devEmbedded/differential_probe/accessories/cable_to_banana/images/cable_to_banana_bottom.png

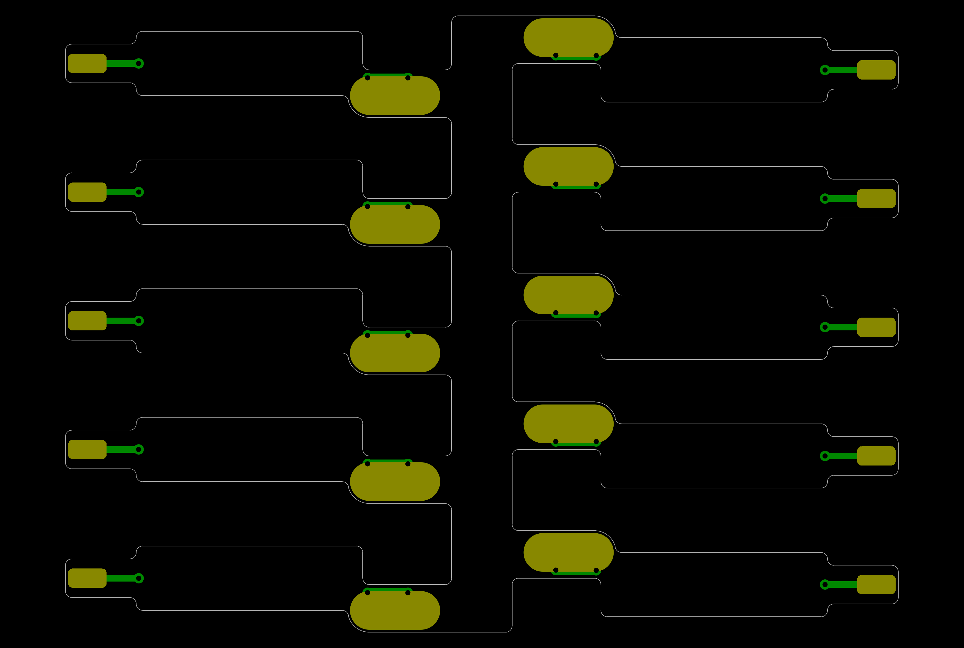
accessories/cable_to_banana/images/cable_to_banana_bottom.png
