devEmbedded/differential_probe/accessories/cable_to_square_pin/images/cable_to_square_pin_bottom.png

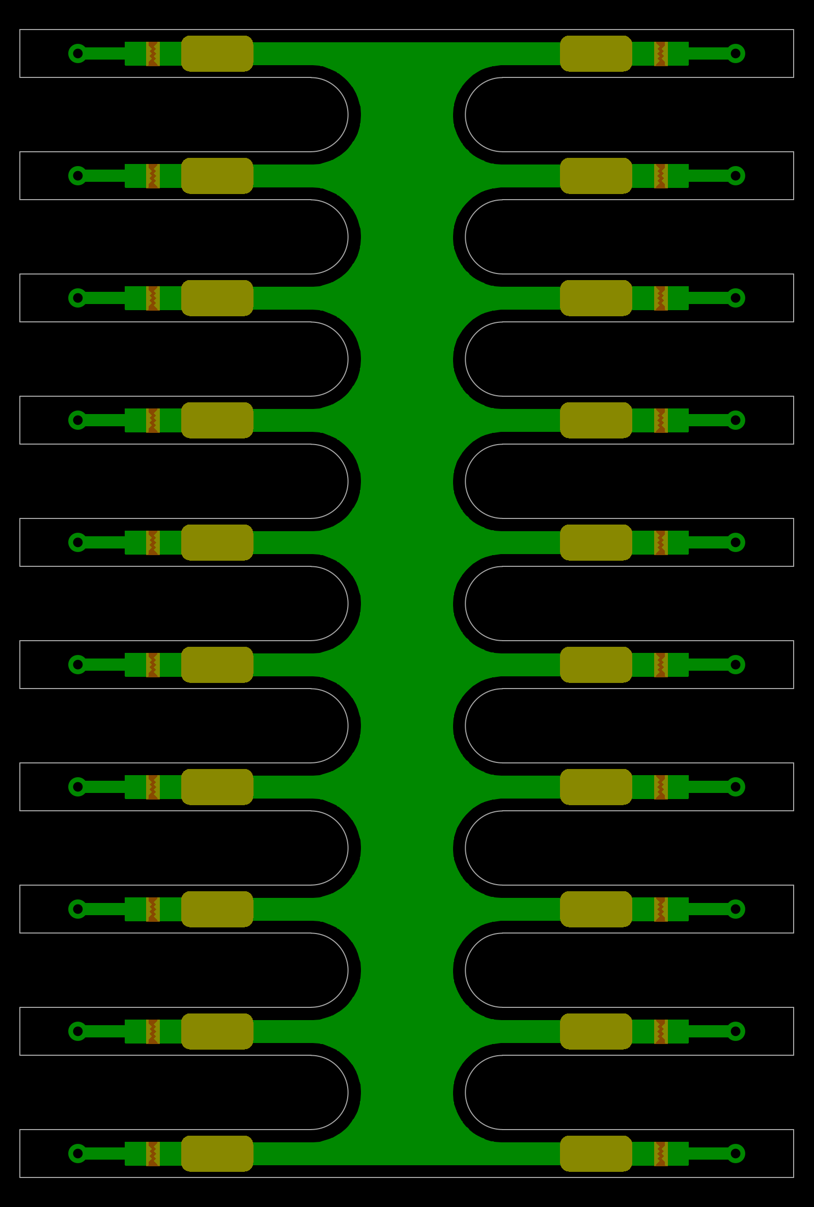
accessories/cable_to_square_pin/images/cable_to_square_pin_bottom.png
