devEmbedded/differential_probe/accessories/cable_to_square_pin/images/cable_to_square_pin_top.png

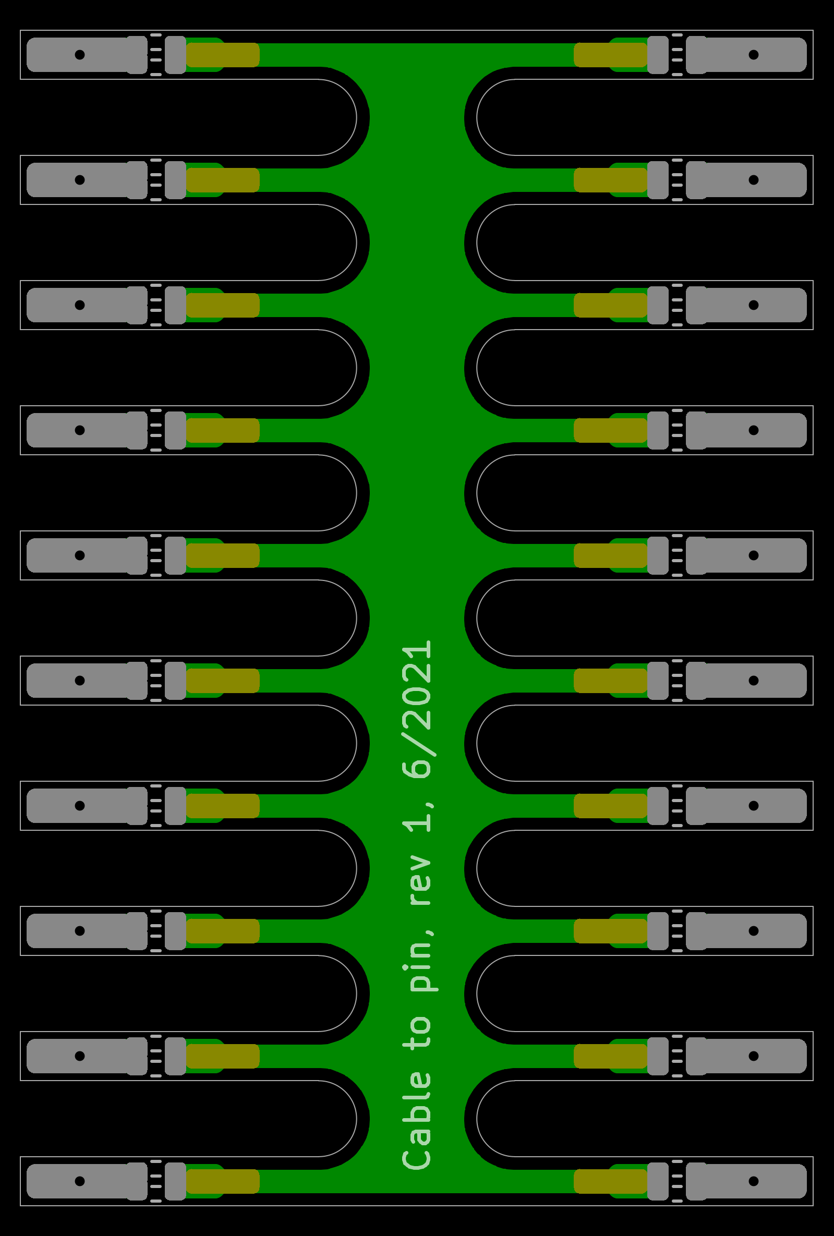
accessories/cable_to_square_pin/images/cable_to_square_pin_top.png
