devEmbedded/differential_probe/accessories/multirange_adapter/frontplate/images/multirange_frontplate_bottom.png

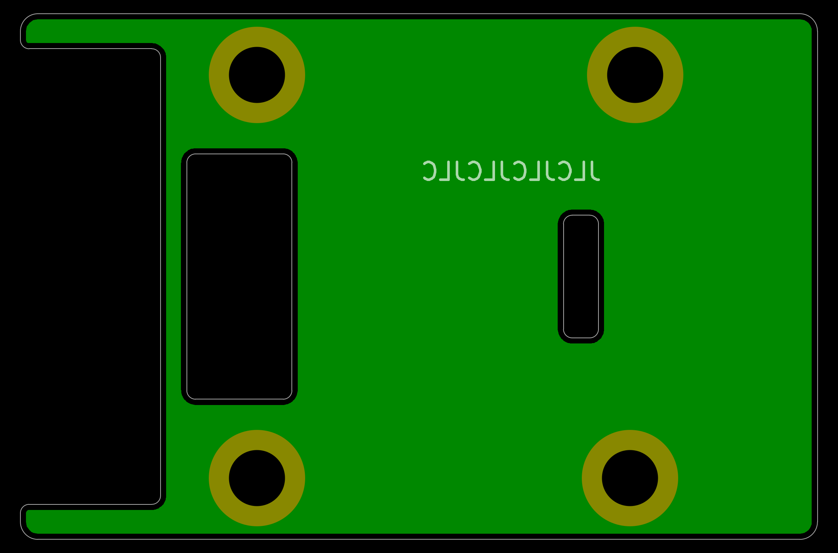
accessories/multirange_adapter/frontplate/images/multirange_frontplate_bottom.png
