devEmbedded/differential_probe/accessories/multirange_adapter/images/multirange_adapter_bottom.png

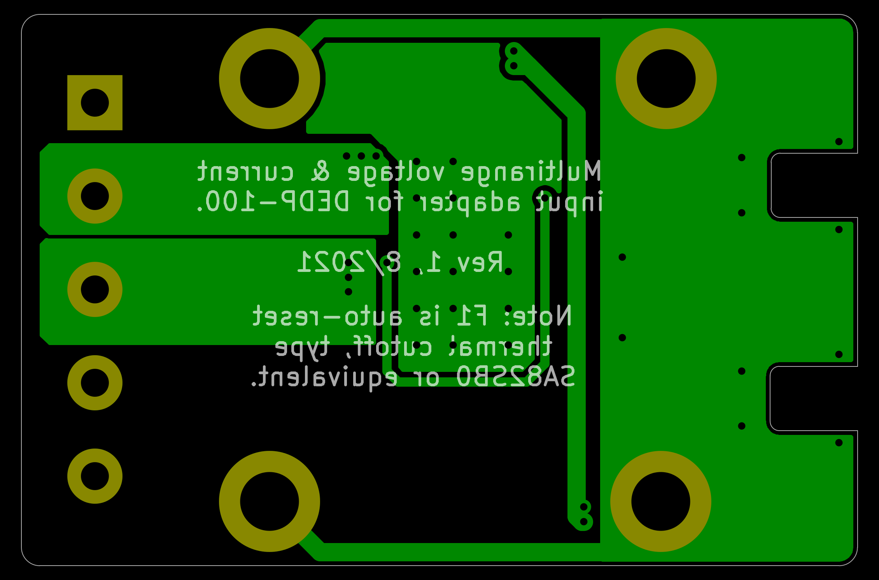
accessories/multirange_adapter/images/multirange_adapter_bottom.png
