devEmbedded/differential_probe/accessories/multirange_adapter/images/multirange_adapter_top.png

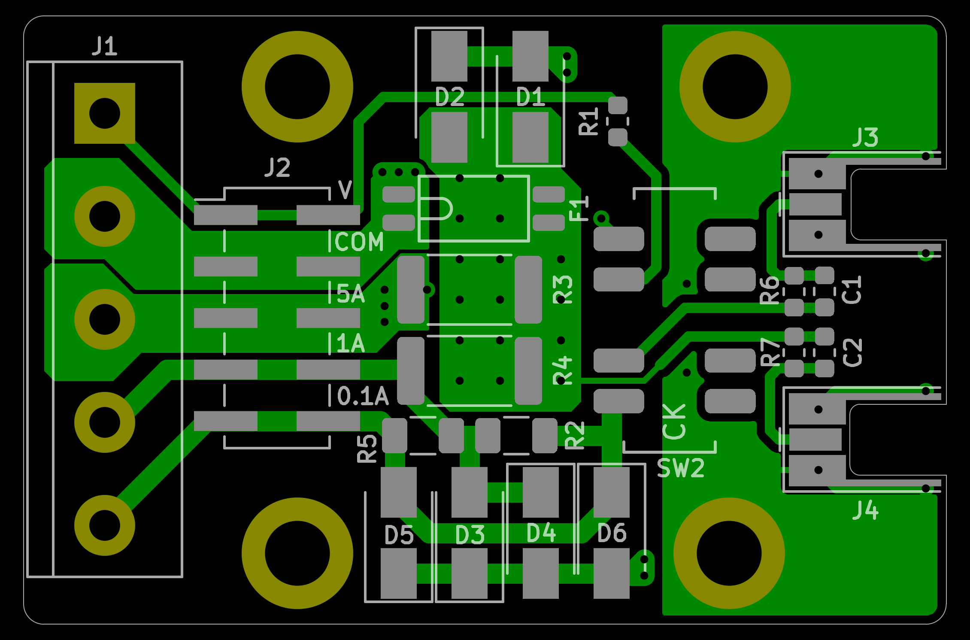
accessories/multirange_adapter/images/multirange_adapter_top.png
