devEmbedded/differential_probe/accessories/tweezer-tips/images/tweezer-tips_bottom.png

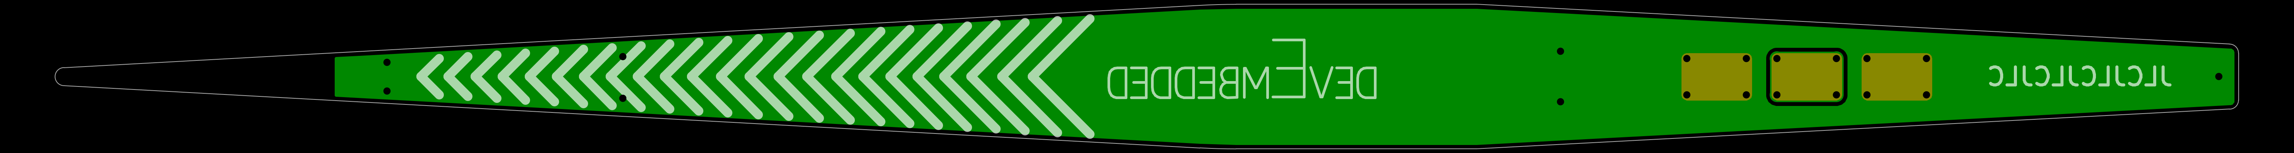
accessories/tweezer-tips/images/tweezer-tips_bottom.png
