devEmbedded/differential_probe/accessories/tweezer-tips/images/tweezer-tips_top.png

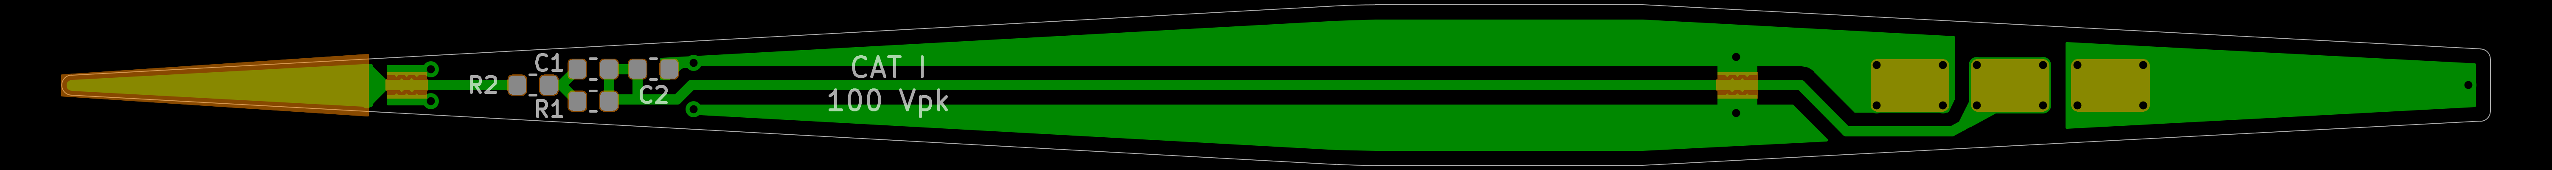
accessories/tweezer-tips/images/tweezer-tips_top.png
