devEmbedded/differential_probe/design_notes/ldo_vs_ferrite_psrr.png

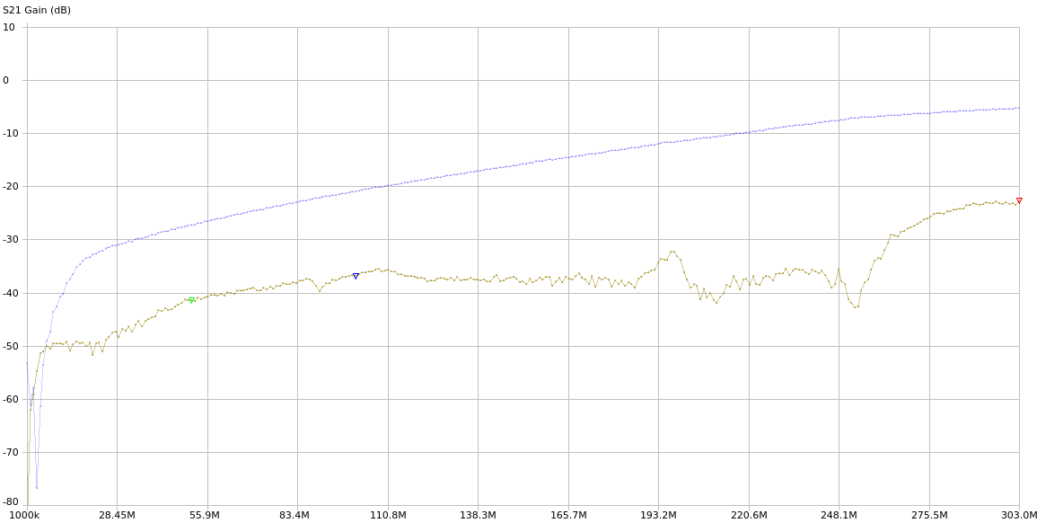
design_notes/ldo_vs_ferrite_psrr.png
