devEmbedded/differential_probe/design_notes/smps_output_fft.png

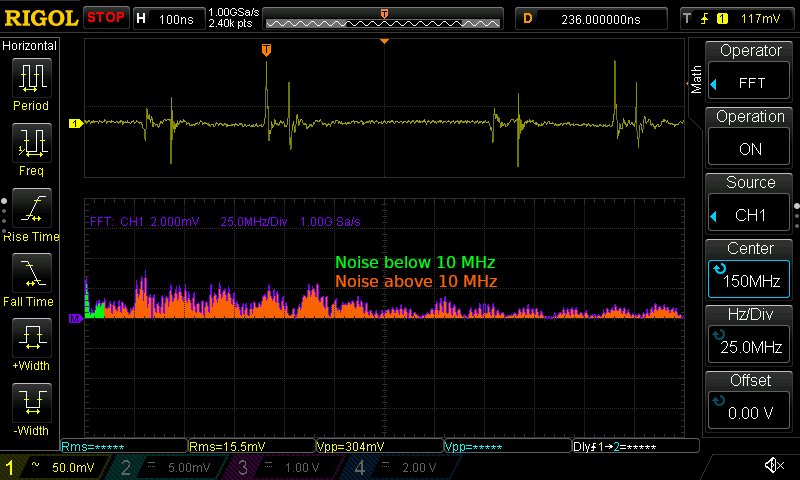
design_notes/smps_output_fft.png
