devEmbedded/differential_probe/diff_probe_amplifier/images/diff_probe_amplifier_bottom.png

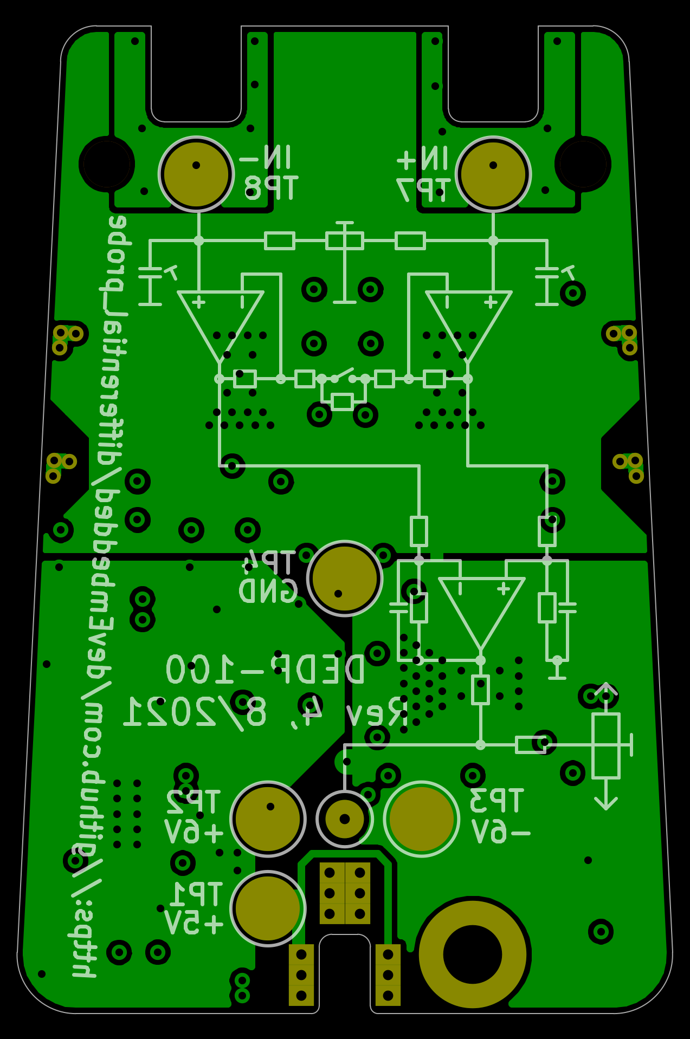
diff_probe_amplifier/images/diff_probe_amplifier_bottom.png
