devEmbedded/differential_probe/diff_probe_amplifier/images/diff_probe_amplifier_mid1.png

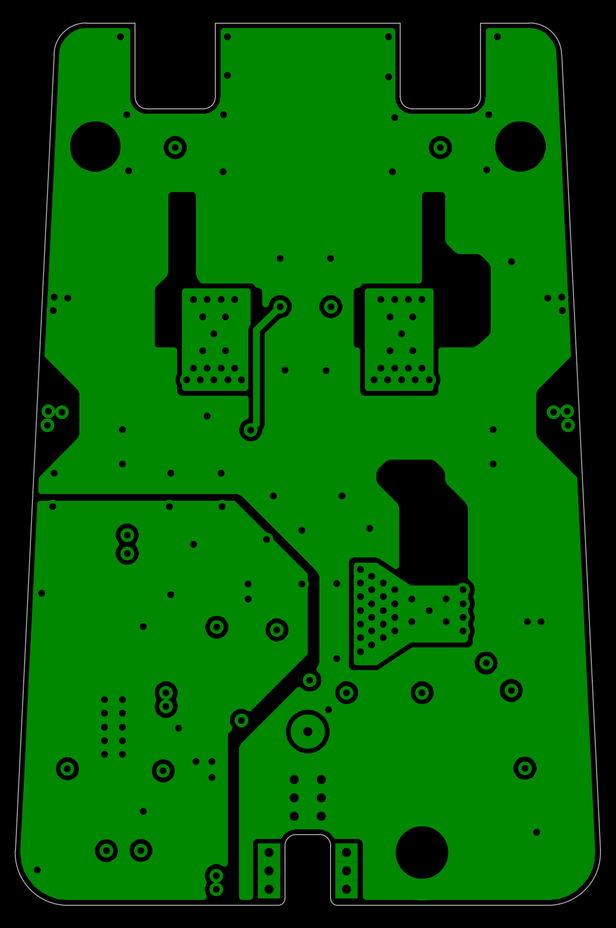
diff_probe_amplifier/images/diff_probe_amplifier_mid1.png
