devEmbedded/differential_probe/diff_probe_amplifier/images/diff_probe_amplifier_render.png

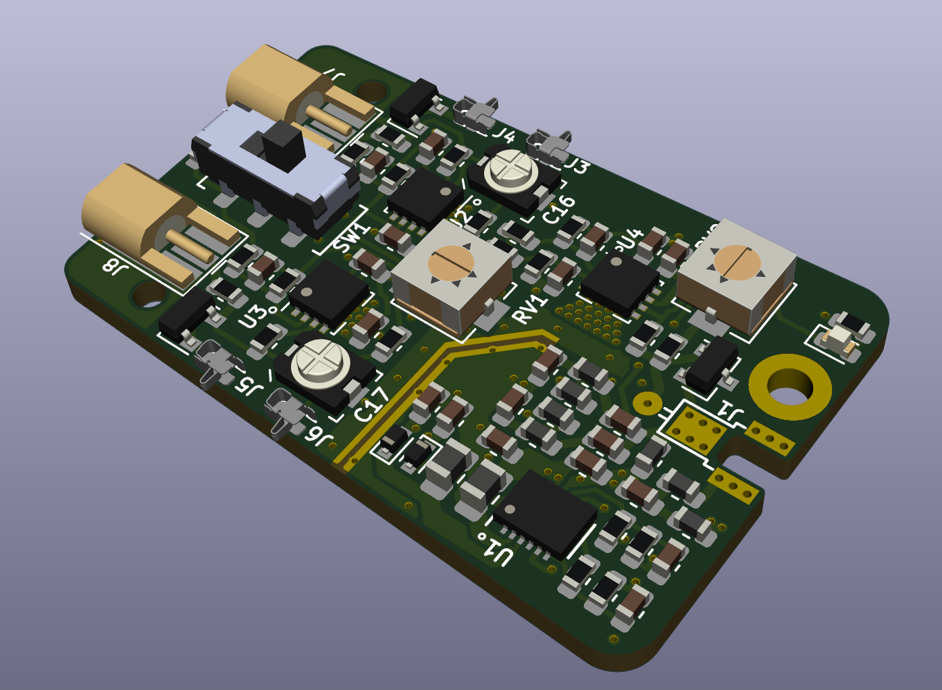
diff_probe_amplifier/images/diff_probe_amplifier_render.png
