devEmbedded/differential_probe/diff_probe_amplifier/images/diff_probe_amplifier_top.png

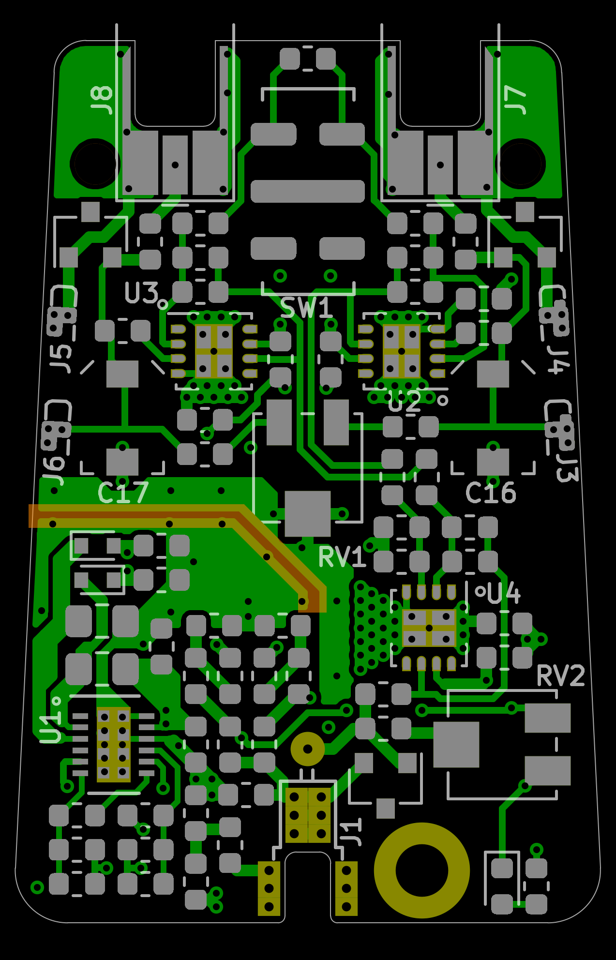
diff_probe_amplifier/images/diff_probe_amplifier_top.png
