devEmbedded/differential_probe/design_notes/psrr_test_circuit.png

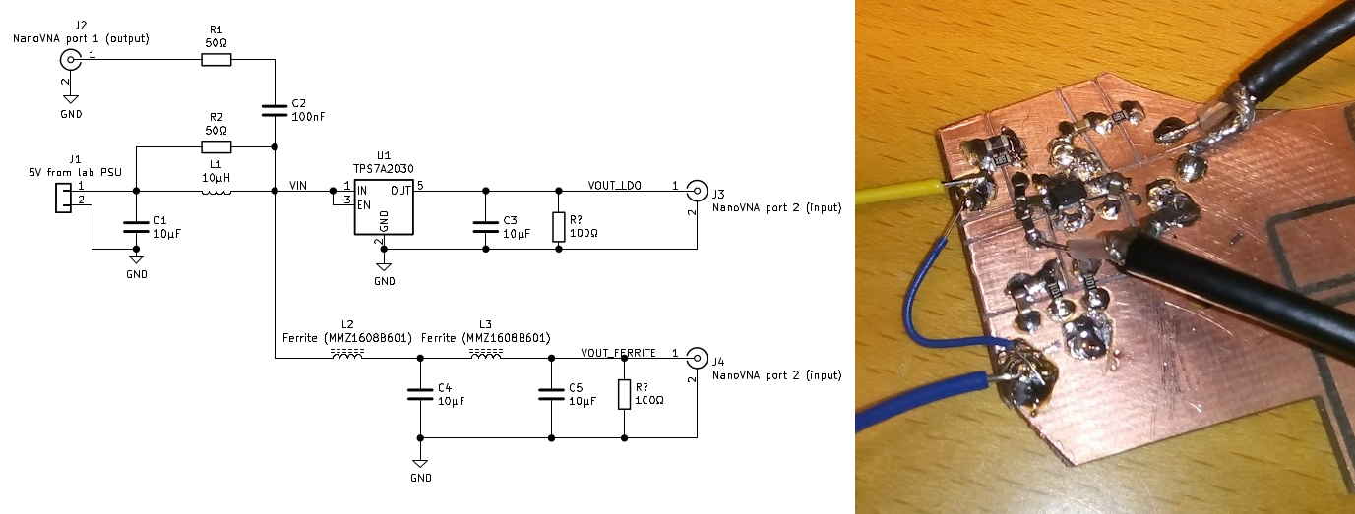
design_notes/psrr_test_circuit.png
